donnels/kerbal-control/3d/Screenshot 2022-02-06 at 22.12.55.png

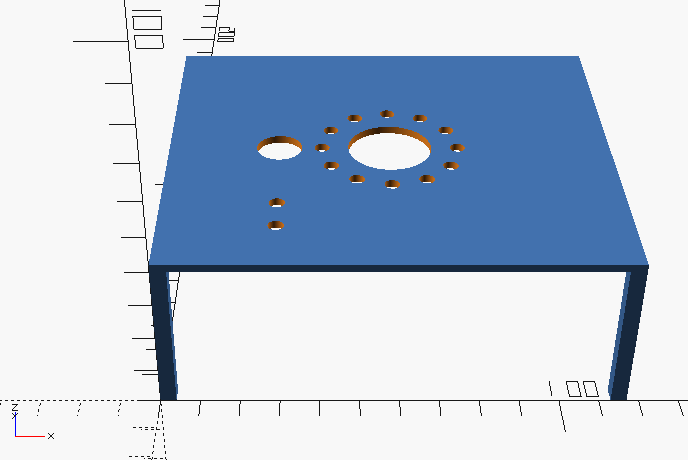
3d/Screenshot 2022-02-06 at 22.12.55.png
