donnels/kerbal-control/3d/Screenshot 2022-02-07 at 20.28.38.png

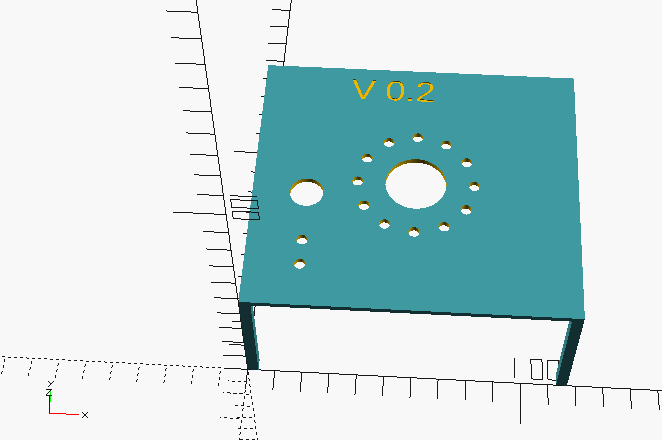
3d/Screenshot 2022-02-07 at 20.28.38.png
