donnels/kerbal-control/images/2022-02-18T14-46%3A09-576Z.png

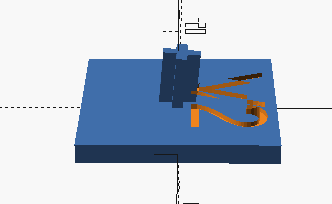
images/2022-02-18T14-46%3A09-576Z.png
