donnels/kerbal-control/src/fastled-test/fastled-test.ino

#include <FastLED.h>
#define NUM_LEDS 22
#define NUM_RING_LEDS 12
#define DATA_PIN 7

CRGB leds[NUM_LEDS];

void setup() { 
    FastLED.addLeds<NEOPIXEL, DATA_PIN>(leds, NUM_LEDS);
    leds[12] = CHSV(0, 255, 16);
    leds[13] = CHSV(33, 255, 16);
    leds[14] = CHSV(65, 255, 16);
    leds[15] = CHSV(97, 255, 16);
    leds[16] = CHSV(129, 255, 16);
    leds[17] = CHSV(161, 255, 16);
    leds[18] = CHSV(193, 255, 16);
    leds[19] = CHSV(225, 255, 16);
    leds[20] = CHSV(255, 255, 16);
    leds[21] = CHSV(255, 255, 16);
    FastLED.show();
}

void loop() {
    for(int dot = 0; dot < NUM_RING_LEDS; dot++) { 
        leds[dot] = CHSV(64, 255, 16);
        FastLED.show();
        // clear this led for the next time around the loop
        leds[dot] = CRGB::Black;
        delay(150);
    }
}
